aleksandr-prilutskiy/SmartHome/src/_EEPROM.ino

//  Filename:     _EEPROM.ino
//  Description:  Система "Умный дом". Блок Smart LPG Sensor. Функции для работы с EEPROM
//  Author:       Aleksandr Prilutskiy
//  Date:         08.11.2019

// Переменные настройки устройства, хранящиеся в EEPROM:
      String        WiFiSSID         =  "";                  // SSID точки доступа WiFi
      String        WiFiPassword     =  "";                  // Пароль для подключения к точке доступа WiFi
      String        MQTT_Server      =  "";                  // DNS-имя или IP-адрес брокера MQTT
      uint16_t      MQTT_Port        =   0;                  // Порт для подключения к брокеру MQTT
      String        MQTT_ID          =  "";                  // ID образца (Instance) брокера MQTT
      String        MQTT_Login       =  "";                  // Логин пользователя брокера MQTT
      String        MQTT_Password    =  "";                  // Пароль пользователя брокера MQTT
      String        MQTT_DeviceID    =  "";                  // ID устройства
      String        MQTT_Temperature =  "";                  // Topic датчика температуры
      String        MQTT_Humidity    =  "";                  // Topic датчика влажности
      String        MQTT_LPG         =  "";                  // Topic датчика углеводородных газов
      uint16_t      alarmLPG         =   0;                  // Порог опасного значения углеводородных газов
      uint8_t       UTC              =   0;                  // Поправка часового пояса

// Константы адресов переменных в EEPROM:
const uint16_t      epprom_WiFiSSID  =   0;                  // WiFiSSID (32 байта)
const uint16_t      epprom_WiFiPass  =  32;                  // WiFiPassword (32 байта)
const uint16_t      epprom_MQTTAddr  =  64;                  // MQTT_Server (62 байта)
const uint16_t      epprom_MQTTPort  = 126;                  // MQTT_Port (2 байта)
const uint16_t      epprom_MQTTID    = 128;                  // MQTT_ID (32 байта)
const uint16_t      epprom_MQTTLogin = 160;                  // MQTT_Login (16 байт)
const uint16_t      epprom_MQTTPass  = 176;                  // MQTT_Password (16 байт)
const uint16_t      epprom_Temperat  = 192;                  // MQTT_Temperature (16 байт)
const uint16_t      epprom_Humidity  = 208;                  // MQTT_Humidity (16 байт)
const uint16_t      epprom_LPG       = 224;                  // MQTT_LPG (16 байт)
const uint16_t      epprom_alarmLPG  = 240;                  // alarmLPG (2 байта)
const uint16_t      epprom_UTC       = 242;                  // UTC (1 байт)

// #FUNCTION# ===================================================================================================
// Name...........: EEPROMReadAll
// Description....: Чтение значений всех переменных из EEPROM
// Syntax.........: EEPROMReadAll()
// ==============================================================================================================
void EEPROMReadAll() {
 EEPROM.begin(sizeEEPROM);
 WiFiSSID         = EEPROMReadString(epprom_WiFiSSID, 32);
 Serial.print(" WiFi SSID = ");
 Serial.println(WiFiSSID);
 WiFiPassword     = EEPROMReadString(epprom_WiFiPass, 32);
 MQTT_Server      = EEPROMReadString(epprom_MQTTAddr, 62);
 MQTT_Port        = EEPROMReadInt(epprom_MQTTPort);
 Serial.print(" MQTT Server = ");
 Serial.print(MQTT_Server);
 Serial.print(":");
 Serial.println(MQTT_Port);
 MQTT_ID          = EEPROMReadString(epprom_MQTTID, 32);
 Serial.print(" MQTT Instance = ");
 Serial.println(MQTT_ID);
 MQTT_Login       = EEPROMReadString(epprom_MQTTLogin, 16);
 Serial.print(" MQTT User = ");
 Serial.println(MQTT_Login);
 MQTT_Password    = EEPROMReadString(epprom_MQTTPass, 16);
 MQTT_Temperature = EEPROMReadString(epprom_Temperat, 16);
 Serial.print(" MQTT Topic Temperature = ");
 Serial.println(MQTT_Temperature);
 MQTT_Humidity    = EEPROMReadString(epprom_Humidity, 16);
 Serial.print(" MQTT Topic Humidity = ");
 Serial.println(MQTT_Humidity);
 MQTT_LPG         = EEPROMReadString(epprom_LPG, 16);
 Serial.print(" MQTT Topic LPG = ");
 Serial.println(MQTT_LPG);
 alarmLPG         = EEPROMReadInt(epprom_alarmLPG);
 Serial.print(" LPG Alarm Level = ");
 Serial.println(alarmLPG);
 UTC              = EEPROMReadByte(epprom_UTC);
 if (UTC == 0) UTC = 24;
 Serial.print(" UTC = ");
 Serial.println(UTC - 24);
 EEPROM.end();
 Serial.println();
} // EEPROMReadAll

// #FUNCTION# ===================================================================================================
// Name...........: EEPROMReadByte
// Description....: Чтение одного байта из EEPROM
// Syntax.........: EEPROMReadByte(startaddr)
// ==============================================================================================================
uint16_t EEPROMReadByte(unsigned int startaddr) {
 return EEPROM.read(startaddr);
} // EEPROMReadByte

// #FUNCTION# ===================================================================================================
// Name...........: EEPROMReadInt
// Description....: Чтение двухбайтного целого числа из EEPROM
// Syntax.........: EEPROMReadInt(startaddr)
// ==============================================================================================================
uint16_t EEPROMReadInt(unsigned int startaddr) {
 return EEPROM.read(startaddr) + 256 * EEPROM.read(startaddr + 1);
} // EEPROMReadInt

// #FUNCTION# ===================================================================================================
// Name...........: EEPROMReadString
// Description....: Чтение строки из EEPROM
// Syntax.........: EEPROMReadString(startaddr, maxlength)
// ==============================================================================================================
String EEPROMReadString(unsigned int startaddr, unsigned int maxlength) {
 String newstr = "";
 byte value;
 for (unsigned int i = 0; i < maxlength; i++) {
  value = EEPROM.read(startaddr + i);
  if (value == 0) break;
  newstr = newstr + char(value);
 }
 return newstr;
} // EEPROMReadString

// #FUNCTION# ===================================================================================================
// Name...........: EEPROMSaveByte
// Description....: Запись в EEPROM одного байта
// Syntax.........: EEPROMSaveByte()
// ==============================================================================================================
void EEPROMSaveByte(uint8_t data, uint8_t& varSetup, String varName, int addr) {
 if (data == varSetup) return;
 varSetup = data;
 EEPROM.write(addr, varSetup);
 Serial.println(varName + " = " + varSetup);
} // EEPROMSaveByte

// #FUNCTION# ===================================================================================================
// Name...........: EEPROMSaveInt
// Description....: Запись в EEPROM двухбайтного целого числа
// Syntax.........: EEPROMSaveInt()
// ==============================================================================================================
void EEPROMSaveInt(uint16_t data, uint16_t& varSetup, String varName, int addr) {
 if (data == varSetup) return;
 varSetup = data;
 EEPROM.write(addr, lowByte(varSetup));
 EEPROM.write(addr + 1, highByte(varSetup));
 Serial.println(varName + " = " + varSetup);
} // EEPROMSaveInt

// #FUNCTION# ===================================================================================================
// Name...........: EEPROMSaveString
// Description....: Запись в EEPROM строки
// Syntax.........: EEPROMSaveString()
// ==============================================================================================================
void EEPROMSaveString(String data, String& varSetup, int maxLength, String varName, int addr) {
 data.replace(" ", "");
 if ((data.length() == 0)||(data == varSetup)) return;
 if (data.length() > maxLength) {
  if (varName.length() > 0)
   errorStr = errorStr + varName + " не должен быть больше " + maxLength + " символов<br>";
  return;
 }
 varSetup = data;
 for (byte i = 0; i < varSetup.length(); i++) EEPROM.write(addr + i, varSetup[i]);
 EEPROM.write(addr + varSetup.length(), 0x00);
 Serial.println(varName + " = " + varSetup);
} // EEPROMSaveString
